Charles-Wuu/EEE-Lunar-Rover-Design-Project-2526/mechanical/cad/parts/upper_case.stl

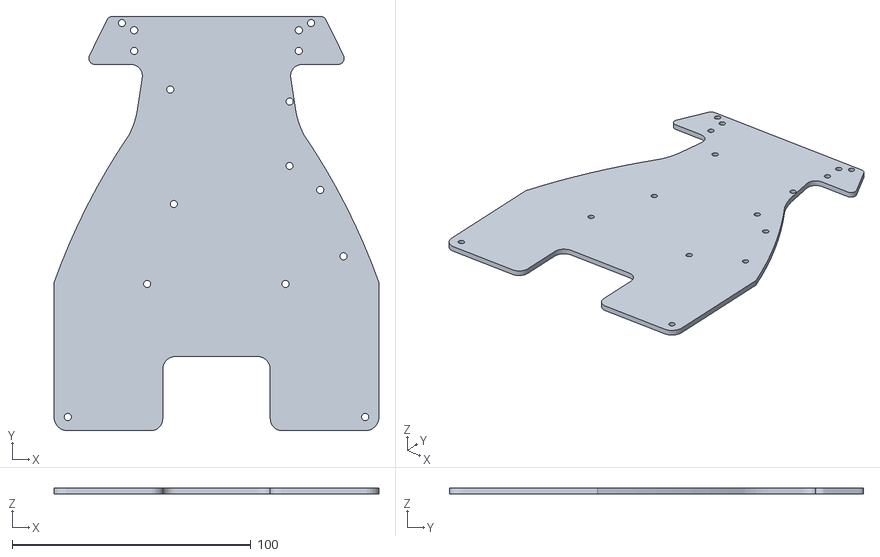
[picture p20: CAD file, 2026-06-26]
mechanical/cad/parts/upper_case.stl
136.2 x 173.6 x 2.50
