Charles-Wuu/EEE-Lunar-Rover-Design-Project-2526/mechanical/cad/parts/front_pla_inner_core_thickened.stl

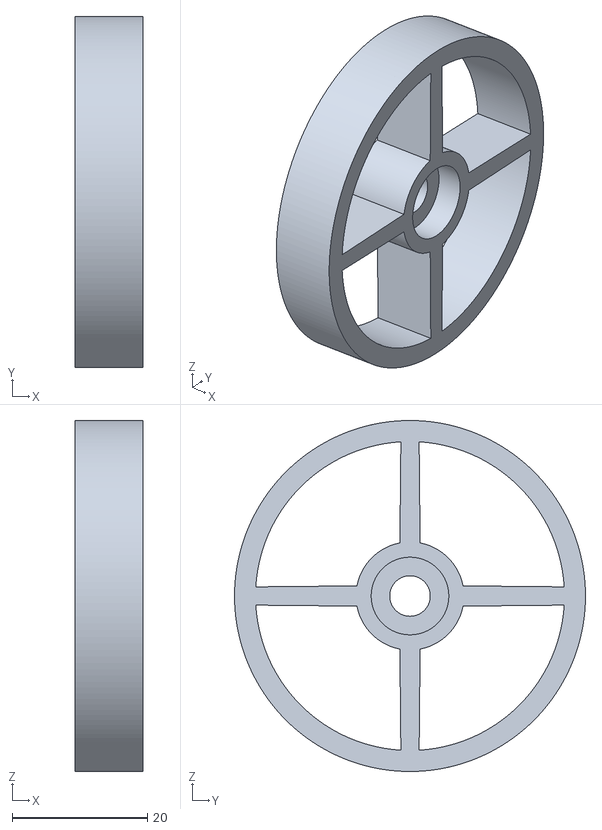
[picture p21: CAD file, 2026-06-26]
mechanical/cad/parts/front_pla_inner_core_thickened.stl
10.0 x 52.0 x 52.0
