Charles-Wuu/EEE-Lunar-Rover-Design-Project-2526/mechanical/cad/parts/rear_wheel_lid.stl

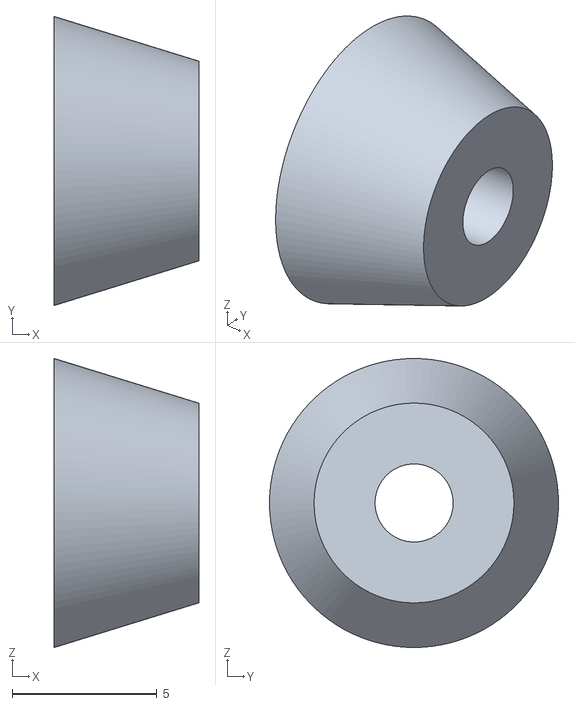
[picture p22: CAD file, 2026-06-26]
mechanical/cad/parts/rear_wheel_lid.stl
5.00 x 10.0 x 10.0
