Charles-Wuu/EEE-Lunar-Rover-Design-Project-2526/mechanical/cad/parts/sensor_mount_v3.stl

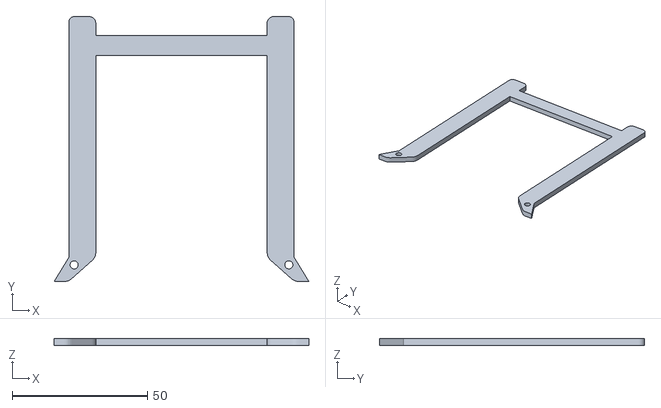
[picture p23: CAD file, 2026-06-26]
mechanical/cad/parts/sensor_mount_v3.stl
94.1 x 97.9 x 2.50
