Charles-Wuu/EEE-Lunar-Rover-Design-Project-2526/mechanical/cad/parts/metro_m0_plate.stl

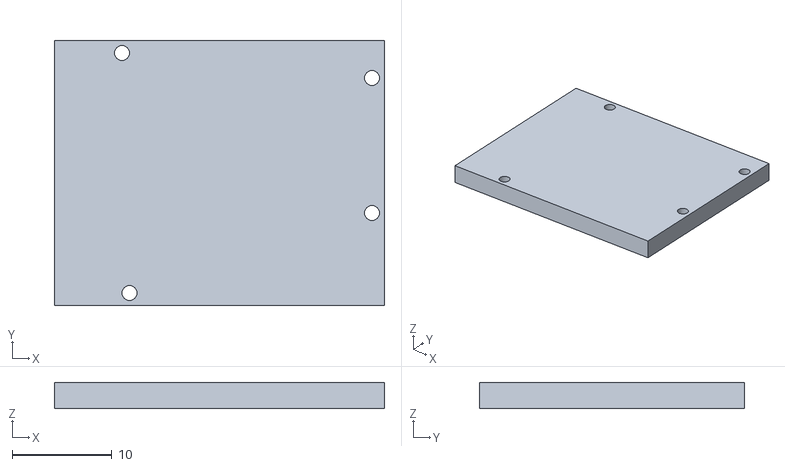
[picture p24: CAD file, 2026-06-26]
mechanical/cad/parts/metro_m0_plate.stl
33.0 x 26.5 x 2.60
