Charles-Wuu/EEE-Lunar-Rover-Design-Project-2526/mechanical/cad/parts/lower_connection.stl

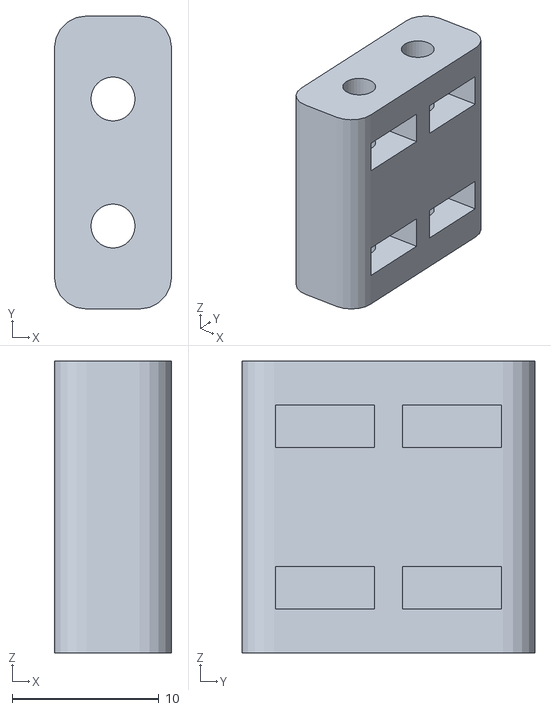
[picture p25: CAD file, 2026-06-26]
mechanical/cad/parts/lower_connection.stl
8.00 x 20.0 x 19.9
