Charles-Wuu/EEE-Lunar-Rover-Design-Project-2526/mechanical/cad/parts/upper_connection.stl

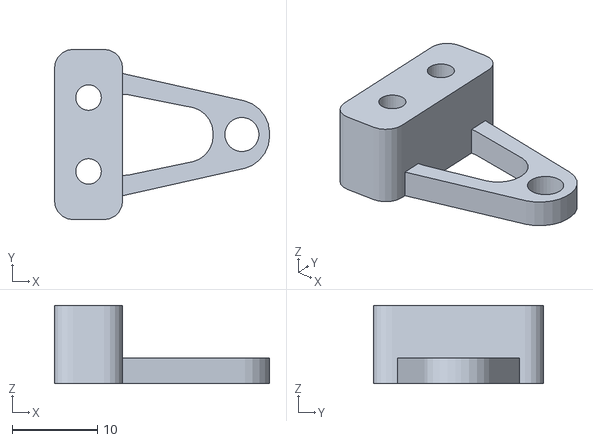
[picture p26: CAD file, 2026-06-26]
mechanical/cad/parts/upper_connection.stl
25.3 x 20.0 x 9.20
