Charles-Wuu/EEE-Lunar-Rover-Design-Project-2526/mechanical/cad/parts/motor_gear.stl

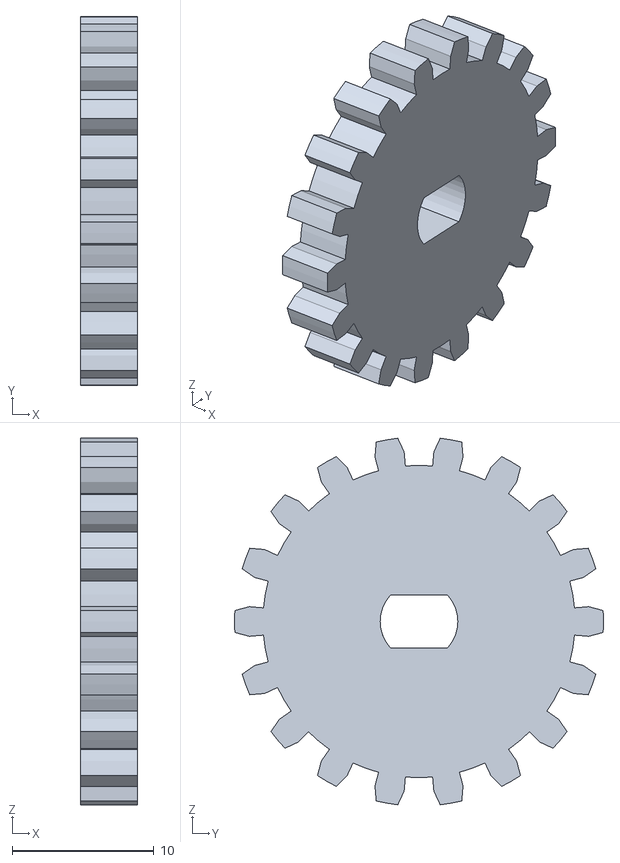
[picture p27: CAD file, 2026-06-26]
mechanical/cad/parts/motor_gear.stl
4.00 x 26.0 x 25.8
