Charles-Wuu/EEE-Lunar-Rover-Design-Project-2526/mechanical/cad/parts/chassis_board.stl

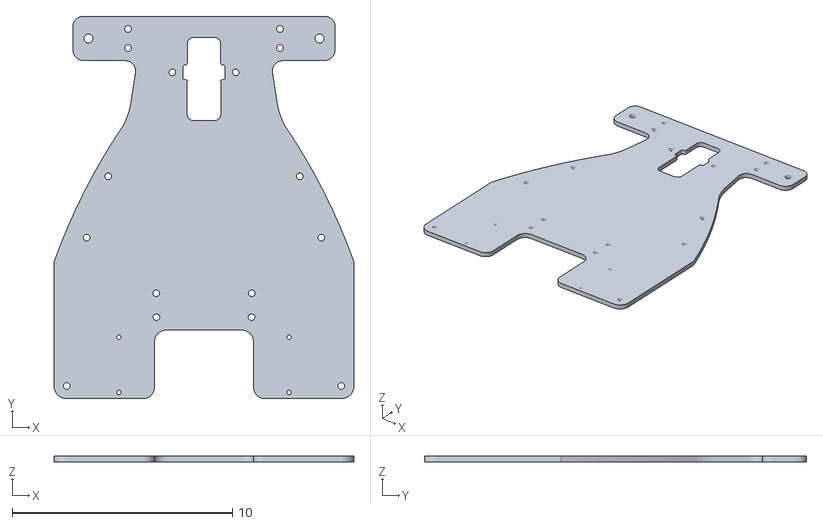
[picture p28: CAD file, 2026-06-26]
mechanical/cad/parts/chassis_board.stl
13.6 x 17.4 x 0.25
